Krayzielilsmoki/Glove80Touchpad/keymaps/vial/config.h

/* SPDX-License-Identifier: GPL-2.0-or-later */
#pragma once

#define VIAL_KEYBOARD_UID { 0xE7, 0xED, 0xFA, 0x35, 0xBB, 0x92, 0x88, 0x33 }

#define VIAL_UNLOCK_COMBO_ROWS { 0, 0 }
#define VIAL_UNLOCK_COMBO_COLS { 0, 1 }
